AlexLymbo/MPPT-ECE445/LTSpiceSim/boost_conv.asc

C1: cap; 447µ
D1: schottky; RB098BM150
GATE: voltage; PULSE(0 15 0 1p 1p .5u 5u)
L1: ind; 0.96µ
M1: nmos; IPT015N10N5
R1: res; 0.1
SOLAR: voltage; 90
V1: voltage; 125
Named nets: Vsw, 0
Vo = Vs/(1-D)
~IL = 0.3*Ioutmax * Vout/Vin = 20.6A
L = (Vin*(Vout-Vin))/(Vout*fs *~IL) = 1.2uH
D = 1 - (Vin*eta)/Vout
20V->120V : D = 0.83
60V -> 102V: D = 0.47
.tran 0.1m
